oldgerman/SCOPE-F07x/HardWare/DataSheets/LCD/1.54寸焊接LCD绘制封装尺寸坑.png

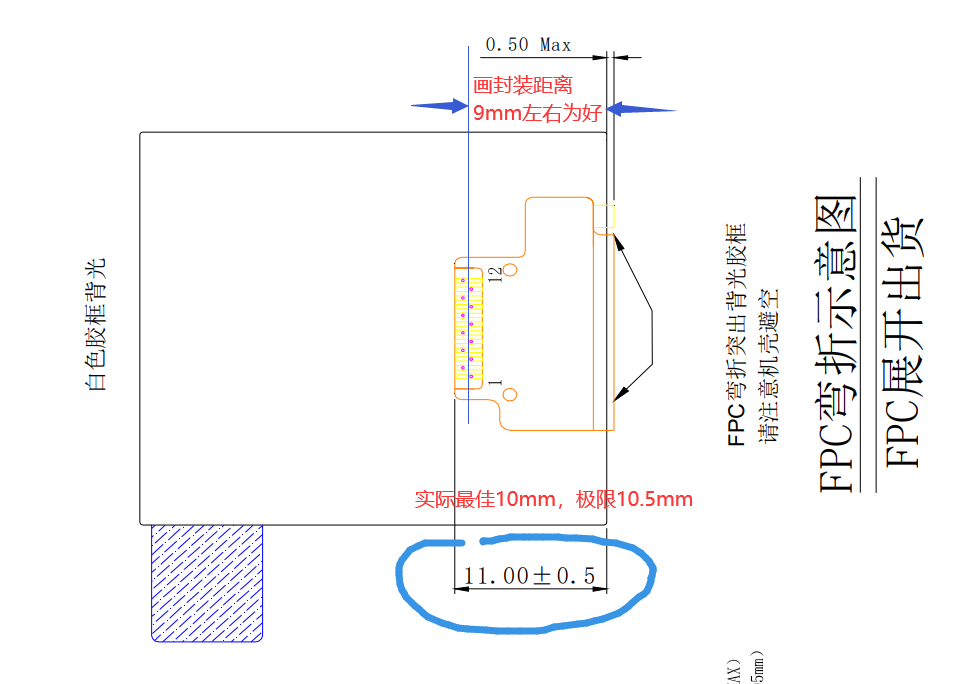
HardWare/DataSheets/LCD/1.54寸焊接LCD绘制封装尺寸坑.png
