oldgerman/SCOPE-F07x/HardWare/DataSheets/电荷泵选型/SGM3204 样板.png

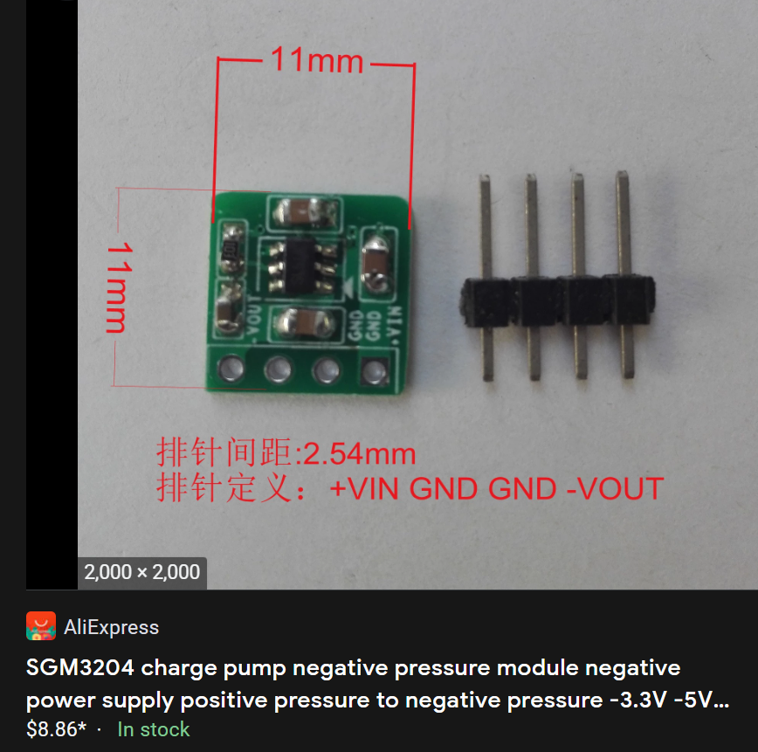
HardWare/DataSheets/电荷泵选型/SGM3204 样板.png
