oldgerman/SCOPE-F07x/HardWare/DataSheets/运放选型/TL974/每通道3.2mA供电.png

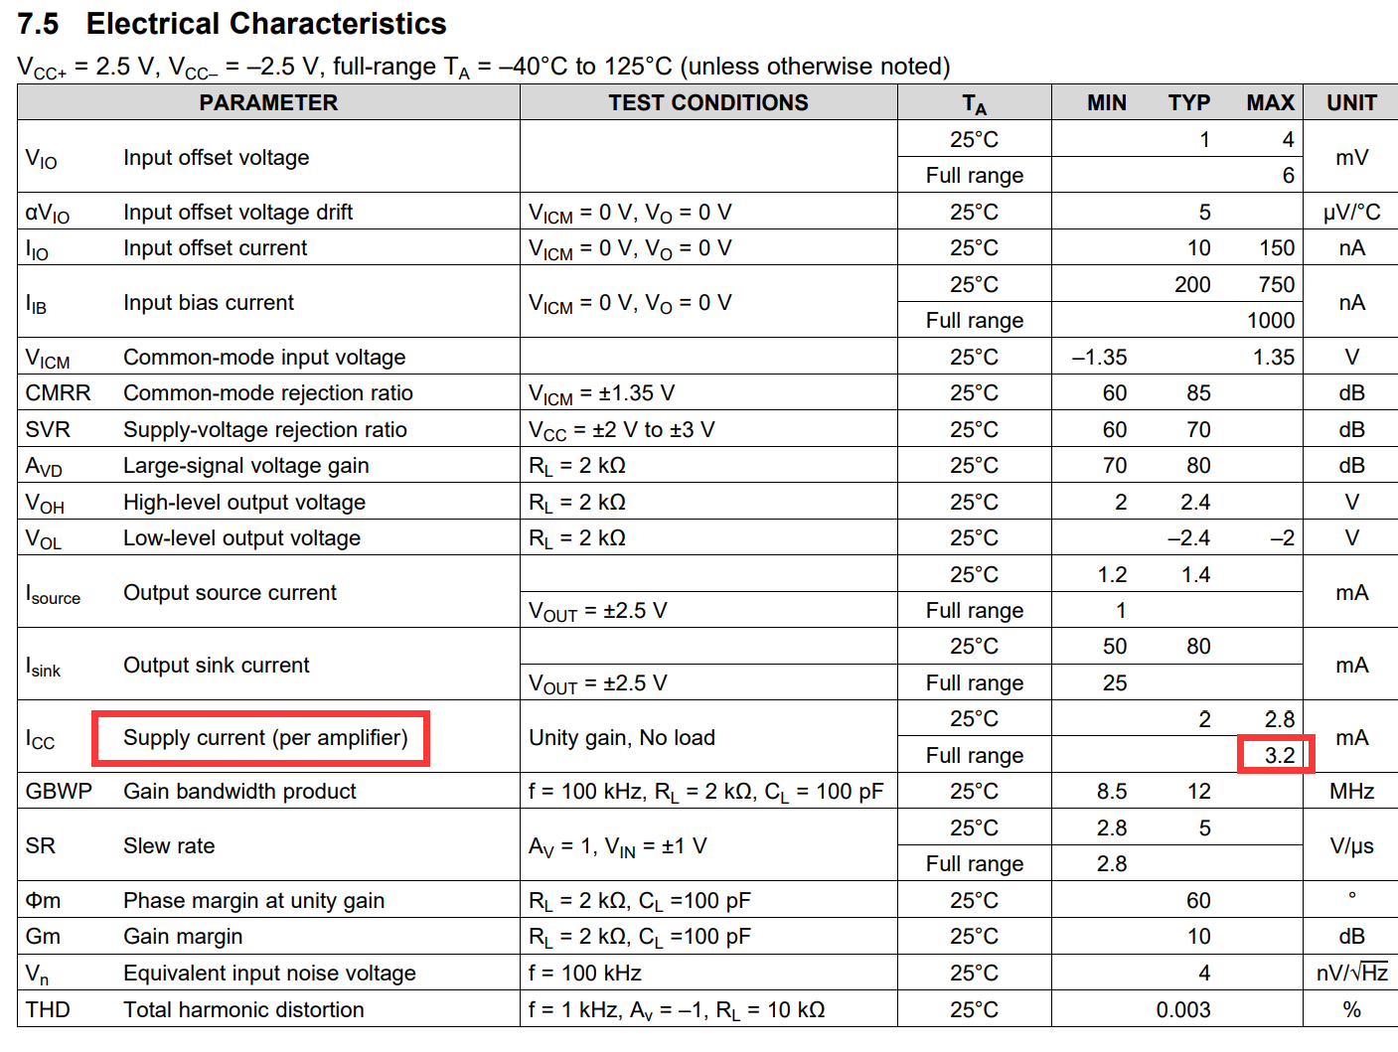
HardWare/DataSheets/运放选型/TL974/每通道3.2mA供电.png
