oldgerman/SCOPE-F07x/HardWare/DataSheets/运放选型/TP2302/长什么样子.JPG

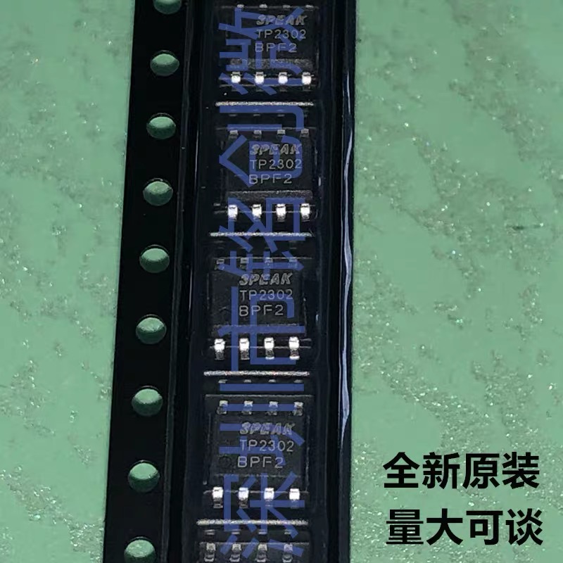
HardWare/DataSheets/运放选型/TP2302/长什么样子.JPG
