oldgerman/SCOPE-F07x/朋友们自驾的成品/20220816_凌.jpg

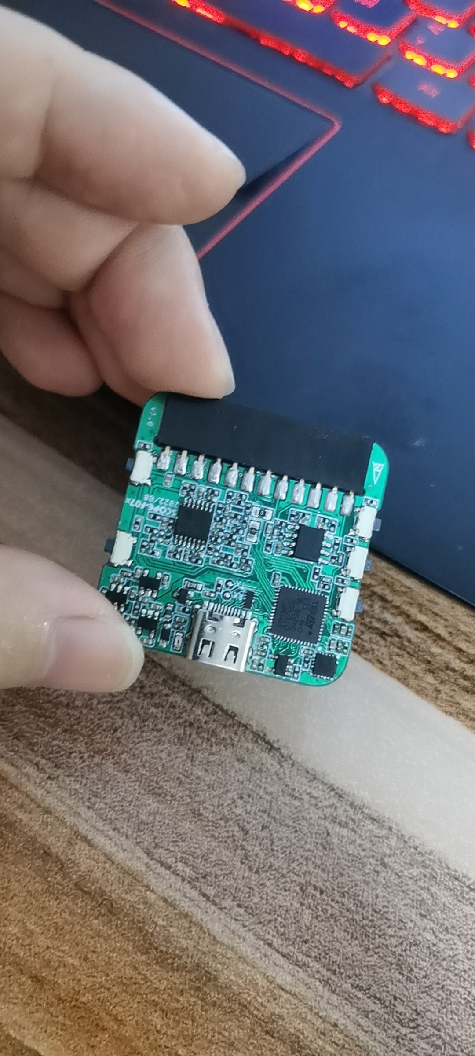
朋友们自驾的成品/20220816_凌.jpg
