oldgerman/SCOPE-F07x/朋友们自驾的成品/20220909_Anthology(2).jpg

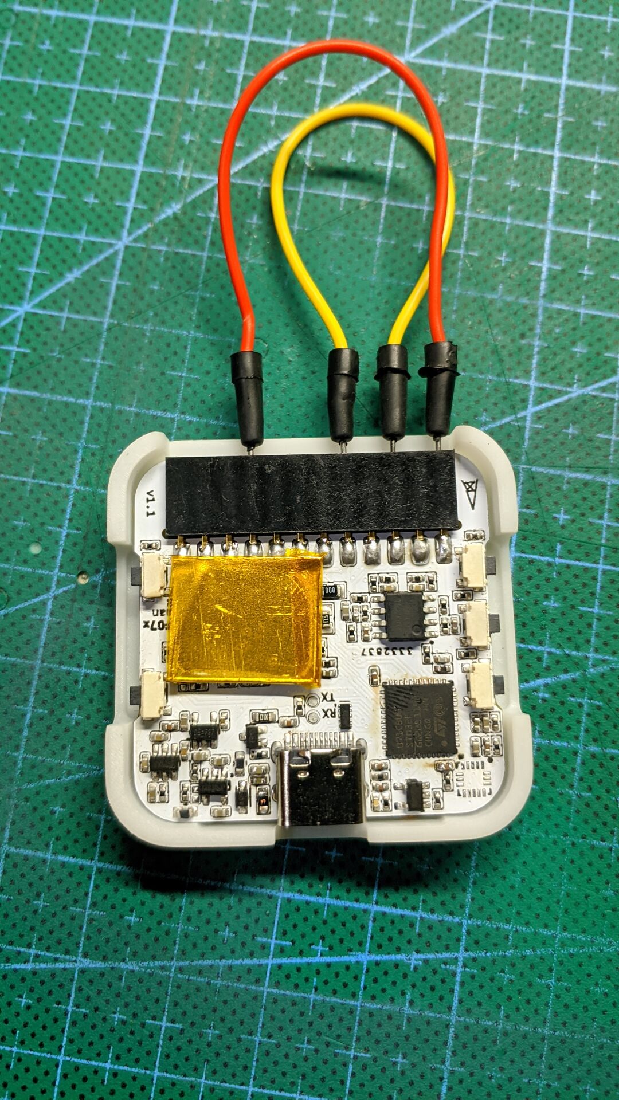
朋友们自驾的成品/20220909_Anthology(2).jpg
