oldgerman/SCOPE-F07x/朋友们自驾的成品/20240320_路(1).jpg

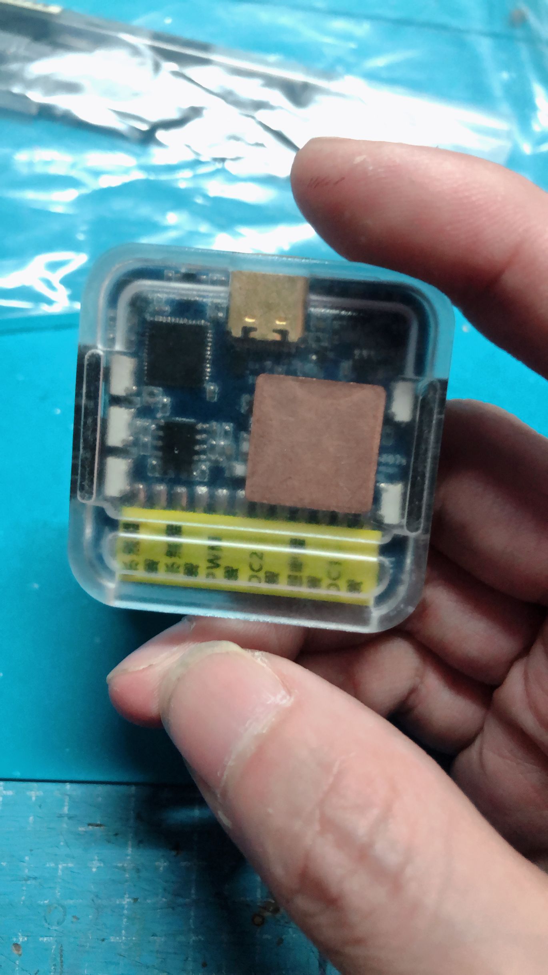
朋友们自驾的成品/20240320_路(1).jpg
