oldgerman/SCOPE-F07x/HardWare/LTspice/TL971_分析_修改为1.65Vand3.3V.asc

C1: cap; 1µ
C2: cap; 150p
C3: cap; 150p
C4: cap; 39p
C5: cap; 1µ
C6: cap; 1µ
C8: cap; 1µ
C10: cap; 1µ
I1: current; 20mA
R1: res; 270r
R2: res; 1k
R3: res; 1k
R4: res; 2k
R5: res; 10k
R6: res; 49.9r
R7: res; 750r
R8: res; 750r
R9: res; 4.3k
R10: res; 1k
R11: res; 3.3K
R13: res; 1k
R14: res; 1k
R15: res; 2k
R16: res; 10k
R18: res; 1.65k
R19: res; 3.3k
R20: res; 12K
R21: res; 11K
R22: res; 1K
U1: OPAx197-Q1
U2: OPAx197-Q1
V1: voltage; 1.65V
V2: voltage; 3.3v
V3: voltage; 5v
V4: voltage; -5v
V5: voltage; SINE(1 0.8 1k 0 0)
V6: voltage; 2.75v
V10: voltage; PULSE(0 3.3 .0 0 0 0.5u 20.83u)
Named nets: 0, PWM_WAV, WAV, WAV_BACK, N5V, P5V, DC_OUT, DC_BACK, PWM_DC_2, P3V3, P1V65, PWM_DC_1
.tran 10m
