oldgerman/SCOPE-F07x/HardWare/LTspice/AD8551_分析.asc

C1: cap; 4.7µF
C2: cap; 0.5pF
R1: res; 1000K
R2: res; 4.7K
R3: res; 3.3K
R4: res; 330K
R5: res; 100R
U1: AD8552
V1: voltage; 1.5v
V2: voltage; 3v
V3: voltage; 5v
V4: voltage; -5v
V5: voltage; PULSE(0 10 .0 0 0 5m 10m)
V6: voltage; 2.75v
V10: voltage; PULSE(3.3 0 .0 0 0 22.7u 100u)
Named nets: 0, N5V, P5V, PWM_DC, P1V5, P3V0, PWM_DC_1, ADC_IN, AIN
.tran 100m
