oldgerman/SCOPE-F07x/HardWare/LTspice/TL971_分析.asc

C1: cap; 1µ
C2: cap; 150p
C3: cap; 150p
C4: cap; 39p
C5: cap; 1µ
C6: cap; 1µ
C8: cap; 1µ
C10: cap; 1µ
R1: res; 270r
R2: res; 1k
R3: res; 1k
R4: res; 2k
R5: res; 10k
R6: res; 49.9r
R7: res; 750r
R8: res; 750r
R9: res; 4.3k
R10: res; 1k
R11: res; 4.7k
R13: res; 1k
R14: res; 1k
R15: res; 2k
R16: res; 10k
R18: res; 1k
R19: res; 2k
R20: res; 12K
R21: res; 33K
R22: res; 2K
U1: ADA4622
U2: ADA4622
V1: voltage; 1.5v
V2: voltage; 3.0v
V3: voltage; 5v
V4: voltage; -5v
V5: voltage; PULSE(0 3.3 .0 0 0 5m 10m)
V6: voltage; 2.75v
V10: voltage; PULSE(0.75 2.75 .0 0 0 15m 30m)
Named nets: 0, PWM_WAV, WAV, WAV_BACK, N5V, P5V, DC_OUT, DC_BACK, PWM_DC, P1V5, P3V0, PWM_DC_1
.tran 30m
